philippmichaelkrebs/FastLapLights/images/basic_testing2.jpg

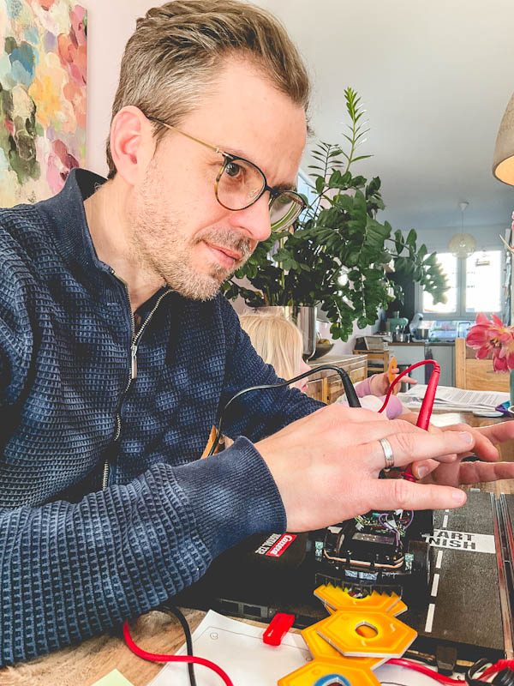
images/basic_testing2.jpg
