philippmichaelkrebs/FastLapLights/images/basic_testing_voltage_divider.jpg

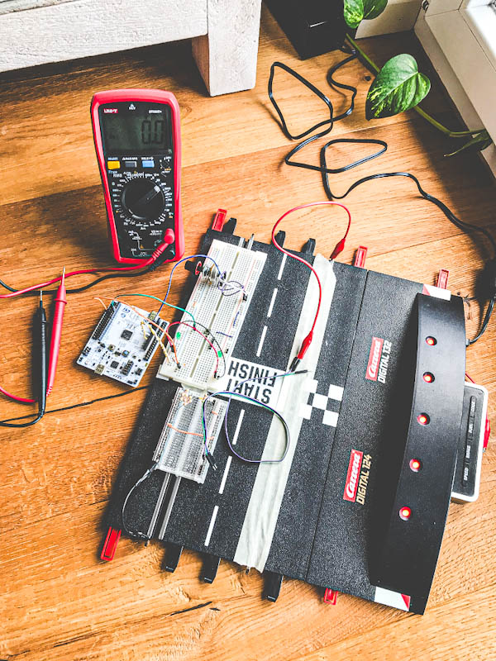
images/basic_testing_voltage_divider.jpg
